Shep-pard/EtherCatIoBoard/EthercatIOBoard/EthercatIOBoard.kicad_sch

## KiCad design EthercatIOBoard/EthercatIOBoard.kicad_sch (2024-12-22)

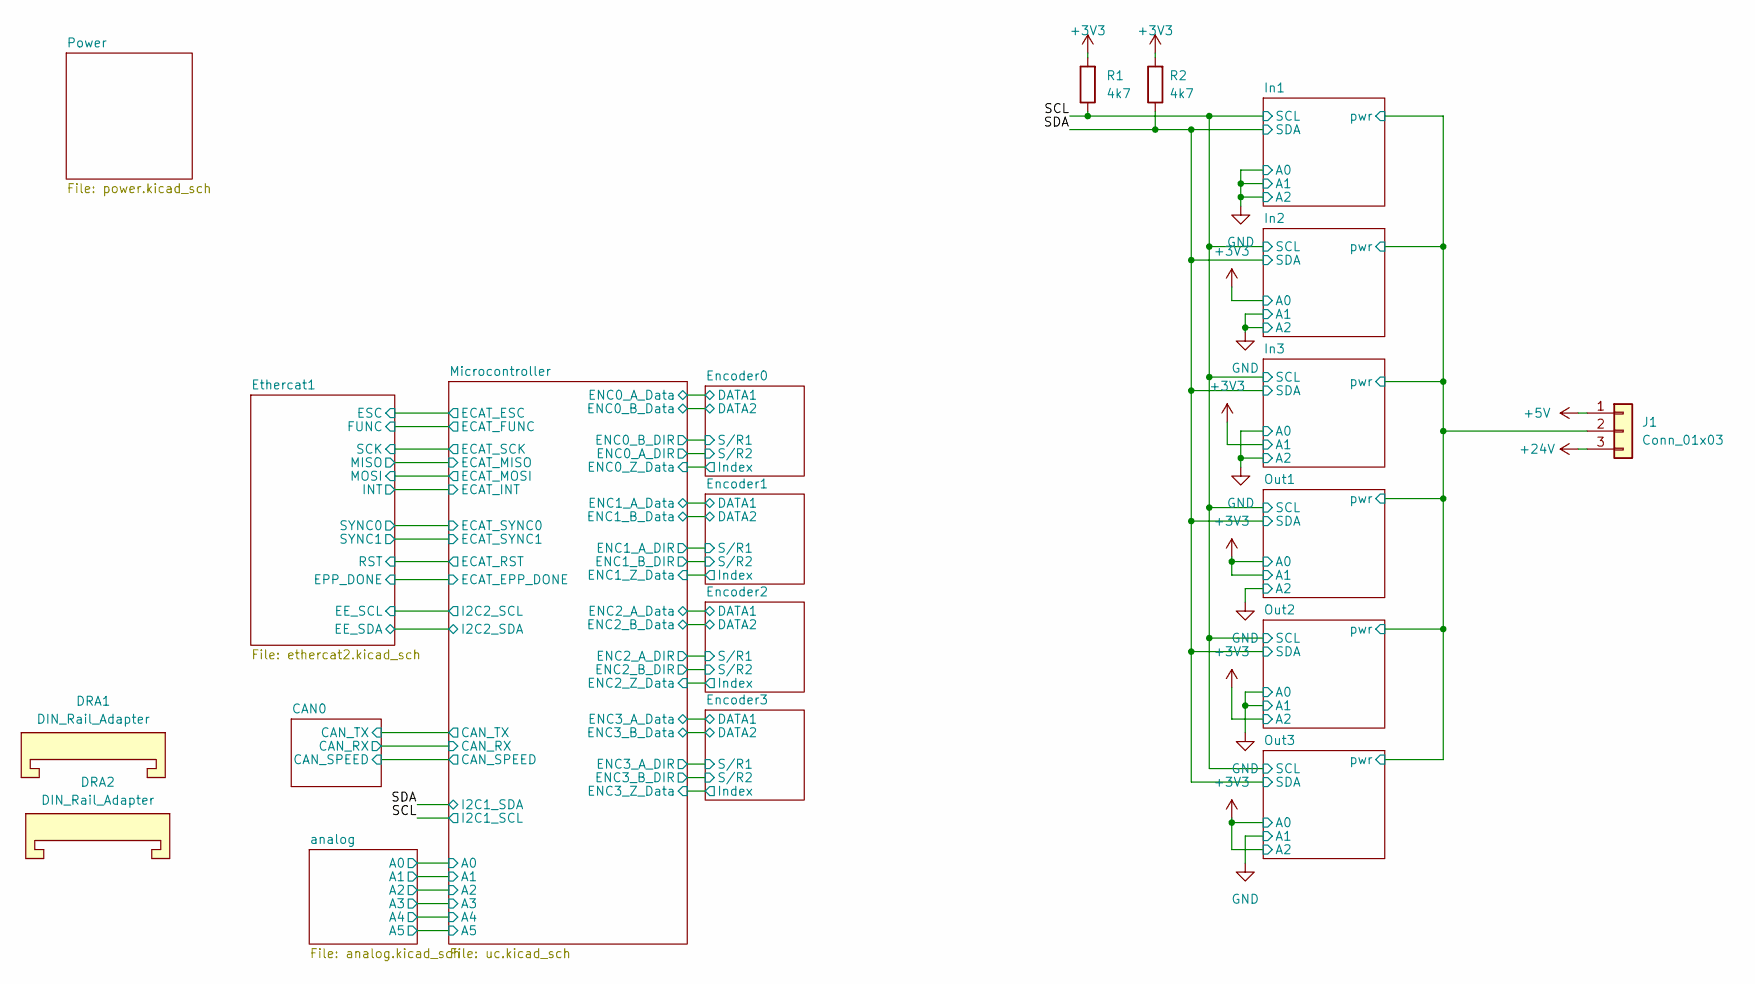
[picture p29: schematic EthercatIOBoard.kicad_sch]

Parts:
DRA1, DRA2: DIN_Rail_Adapter; DINRailAdapter_3xM3_PhoenixContact_1201578
J1: Conn_01x03; PinHeader_1x03_P2.54mm_Vertical_SMD_Pin1Right; JLC C780061
R1, R2: 4k7; R_0402_1005Metric; LCSC Part # C25900

Connections:
+3V3: R1.2, R2.2
+5V: J1.1
+24V: J1.3
SCL: R1.1
SDA: R2.1
pwr: J1.2
