Shep-pard/EtherCatIoBoard/EthercatIOBoard/analog.kicad_sch

## KiCad design EthercatIOBoard/analog.kicad_sch (2024-12-13)

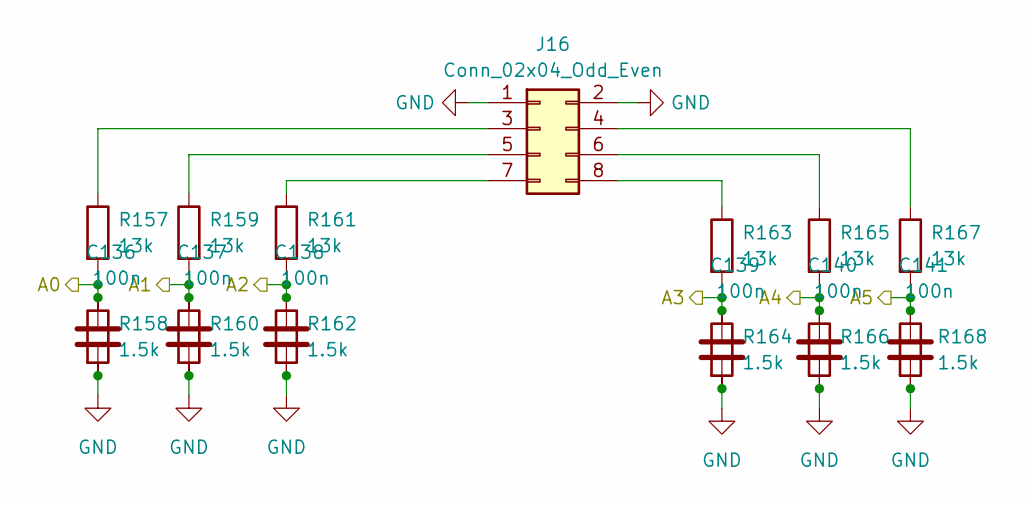
[picture p30: schematic analog.kicad_sch]

Parts:
C136, C137, C138, C139, C140, C141: 100n; C_0402_1005Metric; LCSC Part # C307331
J16: Conn_02x04_Odd_Even; 2Row4Pin3.5mm; LCSC Part # C2923127
R157, R159, R161, R163, R165, R167: 13k; R_0603_1608Metric; LCSC Part # C22797
R158, R160, R162: 1.5k; R_0603_1608Metric; LCSC Part # C22843
R164, R166, R168: 1.5k; R_0603_1608Metric; LCSC Part # C22797

Connections:
A0: C136.1, R157.2, R158.1
A1: C137.1, R159.2, R160.1
A2: C138.1, R161.2, R162.1
A3: C139.1, R163.2, R164.1
A4: C140.1, R165.2, R166.1
A5: C141.1, R167.2, R168.1
GND: C136.2, C137.2, C138.2, C139.2, C140.2, C141.2, J16.1, J16.2, R158.2, R160.2, R162.2, R164.2, R166.2, R168.2
unnamed: J16.3, R157.1
unnamed: J16.4, R167.1
unnamed: J16.5, R159.1
unnamed: J16.6, R165.1
unnamed: J16.7, R161.1
unnamed: J16.8, R163.1
