Shep-pard/EtherCatIoBoard/EthercatIOBoard/can.kicad_sch

## KiCad design EthercatIOBoard/can.kicad_sch (2024-12-13)

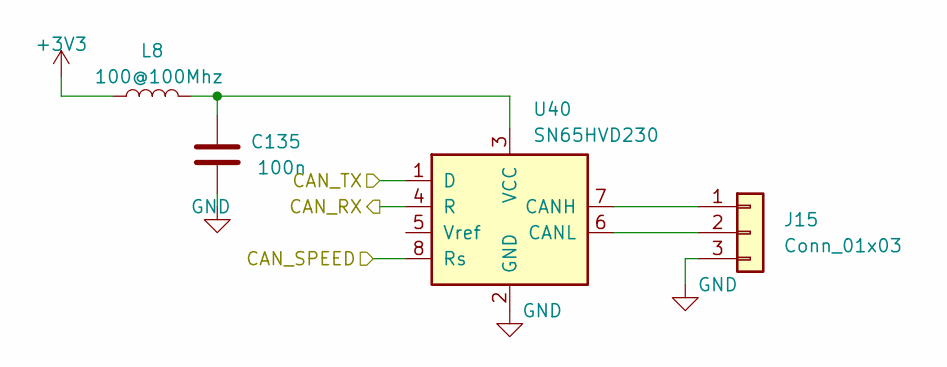
[picture p31: schematic can.kicad_sch]

Parts:
C135: 100n; C_0402_1005Metric; LCSC Part # C307331
J15: Conn_01x03; TerminalBlock_4Ucon_1x03_P3.50mm_Vertical; LCSC Part # C192778
L8: 100@100Mhz; R_0805_2012Metric; LCSC Part # C1015
U40: SN65HVD230; SOIC-8_3.9x4.9mm_P1.27mm; LCSC Part # C12084

Connections:
+3V3: L8.1
CAN_RX: U40.4 (R)
CAN_SPEED: U40.8 (Rs)
CAN_TX: U40.1 (D)
GND: C135.2, J15.3, U40.2 (GND)
unnamed: C135.1, L8.2, U40.3 (VCC)
unnamed: J15.1, U40.7 (CANH)
unnamed: J15.2, U40.6 (CANL)
