Shep-pard/EtherCatIoBoard/EthercatIOBoard/digIn.kicad_sch

## KiCad design EthercatIOBoard/digIn.kicad_sch (2024-12-13)

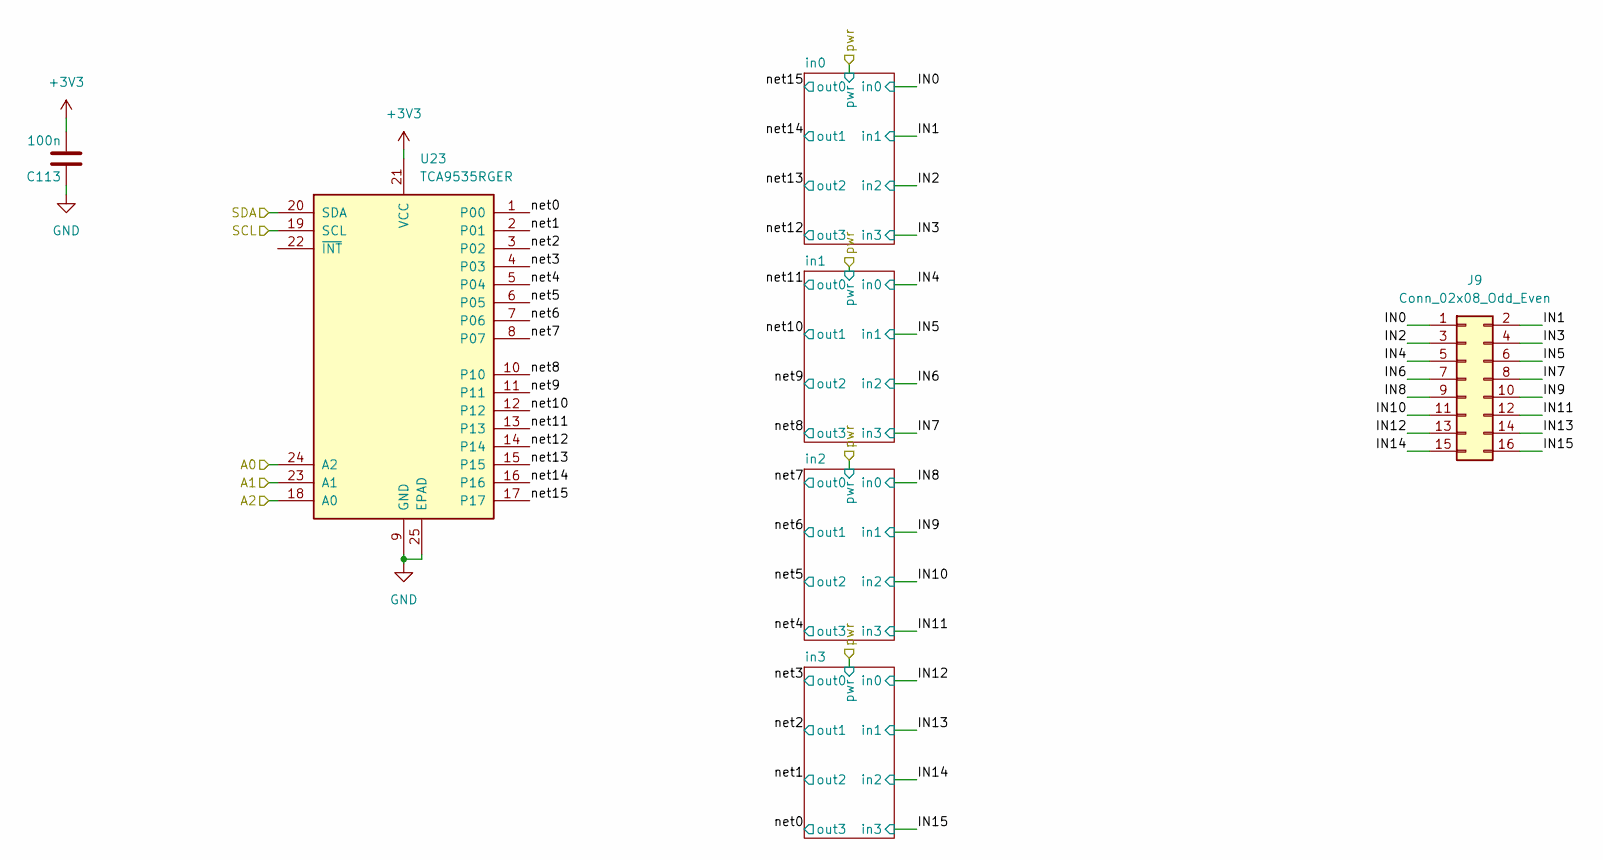
[picture p32: schematic digIn.kicad_sch]

Parts:
C113: 100n; C_0402_1005Metric; LCSC Part # C307331
J9: Conn_02x08_Odd_Even; 2Row8Pin3.5mm; LCSC Part # C2923113
U23: TCA9535RGER; VQFN-24-1EP_4x4mm_P0.5mm_EP2.45x2.45mm; JLC C527428

Connections:
+3V3: C113.2, U23.21 (VCC)
A0: U23.24 (A2)
A1: U23.23 (A1)
A2: U23.18 (A0)
GND: C113.1, U23.9 (GND), U23.25 (EPAD)
IN0: J9.1
IN1: J9.2
IN2: J9.3
IN3: J9.4
IN4: J9.5
IN5: J9.6
IN6: J9.7
IN7: J9.8
IN8: J9.9
IN9: J9.10
IN10: J9.11
IN11: J9.12
IN12: J9.13
IN13: J9.14
IN14: J9.15
IN15: J9.16
SCL: U23.19 (SCL)
SDA: U23.20 (SDA)
net0: U23.1 (P00)
net1: U23.2 (P01)
net2: U23.3 (P02)
net3: U23.4 (P03)
net4: U23.5 (P04)
net5: U23.6 (P05)
net6: U23.7 (P06)
net7: U23.8 (P07)
net8: U23.10
net9: U23.11
net10: U23.12
net11: U23.13
net12: U23.14
net13: U23.15
net14: U23.16
net15: U23.17
