Shep-pard/EtherCatIoBoard/EthercatIOBoard/digInSingle.kicad_sch

## KiCad design EthercatIOBoard/digInSingle.kicad_sch (2024-12-13)

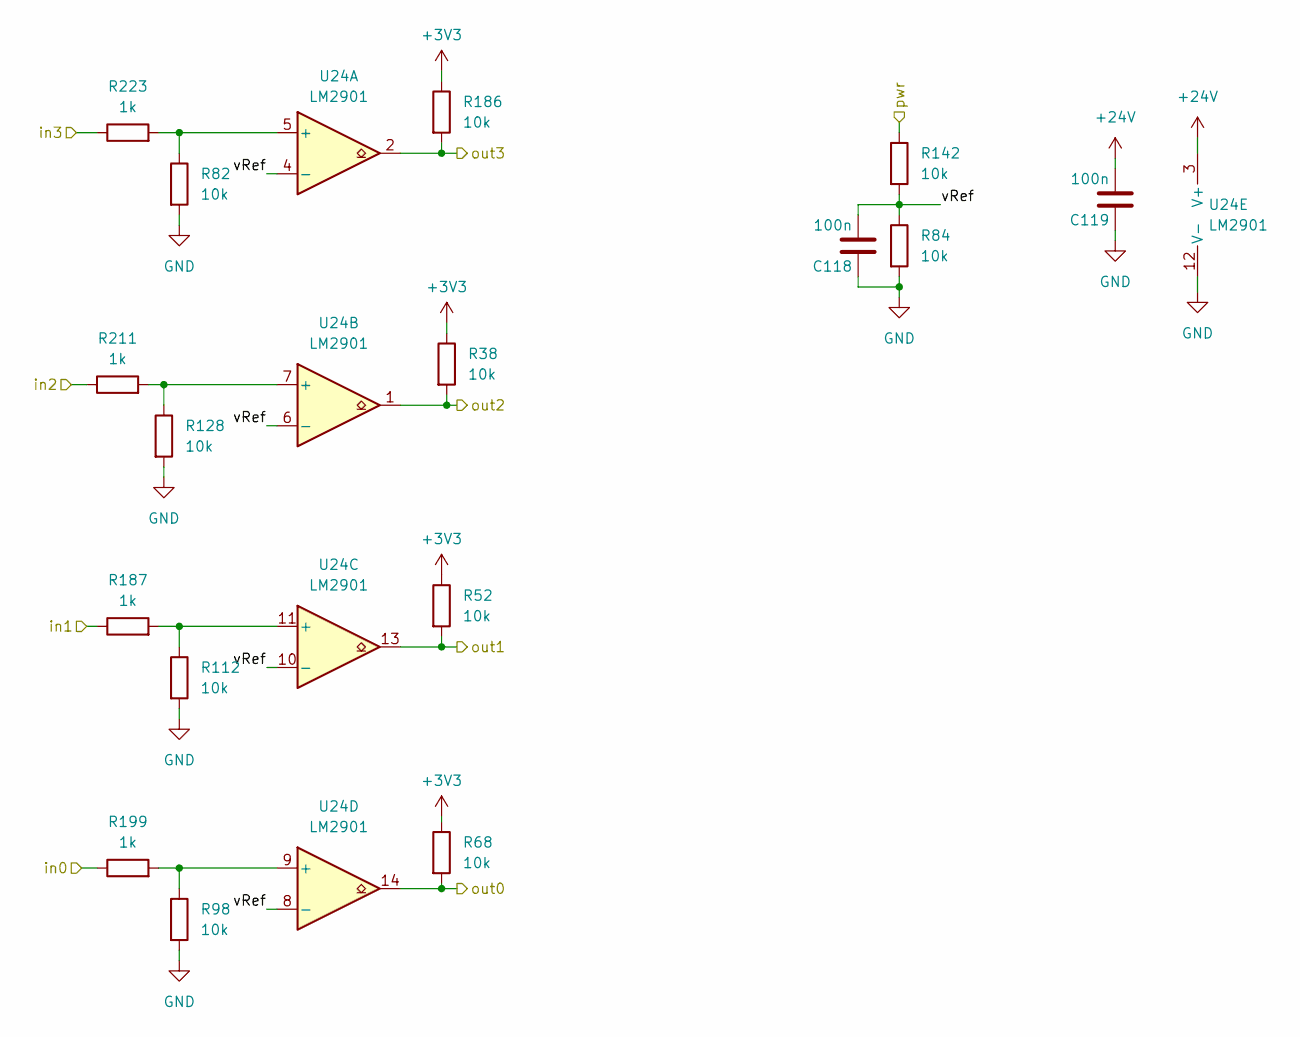
[picture p33: schematic digInSingle.kicad_sch]

Parts:
C118, C119: 100n; C_0402_1005Metric; LCSC Part # C307331
R38, R52, R68, R82, R84, R98, R112, R128, R142, R186: 10k; C_0402_1005Metric; LCSC Part # C25744
R187, R199, R211, R223: 1k; C_0402_1005Metric; LCSC Part # C11702
U24: LM2901; SO-14_3.9x8.65mm_P1.27mm; LCSC Part # C5145307

Connections:
+3V3: R38.1, R52.1, R68.1, R186.1
+24V: C119.2, U24.3 (V+)
GND: C118.1, C119.1, R82.2, R84.2, R98.2, R112.2, R128.2, U24.12 (V-)
unnamed: R112.1, R187.2, U24.11 (+)
unnamed: R128.1, R211.2, U24.7 (+)
unnamed: R98.1, R199.2, U24.9 (+)
unnamed: R82.1, R223.2, U24.5 (+)
in0: R199.1
in1: R187.1
in2: R211.1
in3: R223.1
out0: R68.2, U24.14
out1: R52.2, U24.13
out2: R38.2, U24.1
out3: R186.2, U24.2
pwr: R142.1
vRef: C118.2, R84.1, R142.2, U24.4 (-), U24.6 (-), U24.8 (-), U24.10 (-)
