Shep-pard/EtherCatIoBoard/EthercatIOBoard/digOut.kicad_sch

## KiCad design EthercatIOBoard/digOut.kicad_sch (2024-12-13)

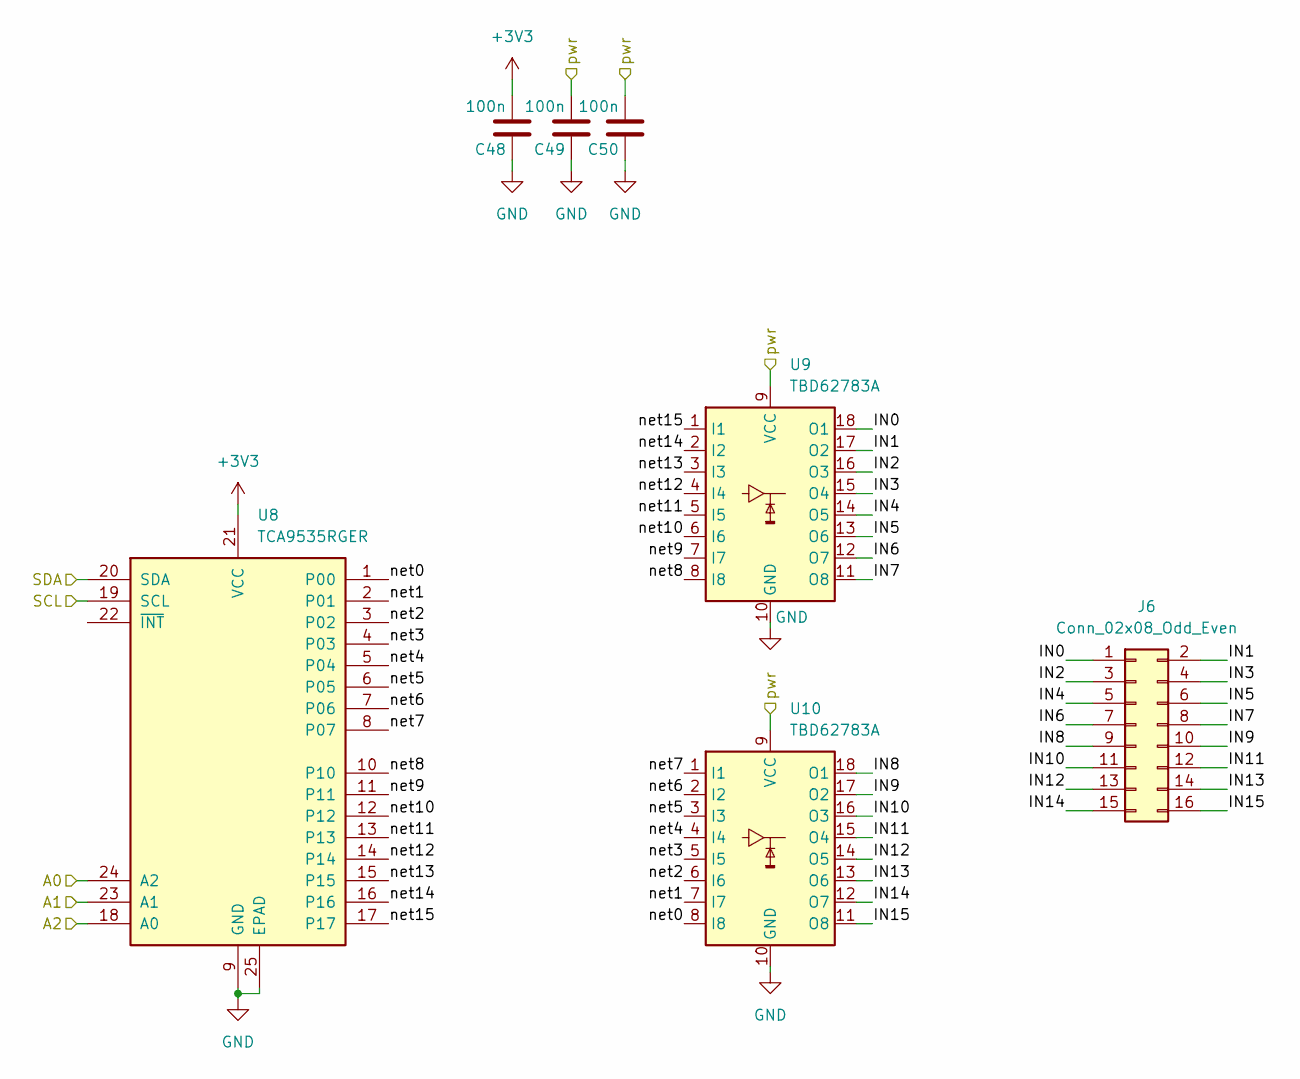
[picture p34: schematic digOut.kicad_sch]

Parts:
C48, C49, C50: 100n; C_0402_1005Metric; LCSC Part # C307331
J6: Conn_02x08_Odd_Even; 2Row8Pin3.5mm; LCSC Part # C2923113
U8: TCA9535RGER; VQFN-24-1EP_4x4mm_P0.5mm_EP2.45x2.45mm; JLC C527428
U9, U10: TBD62783A; SOP-18_7x12.5mm_P1.27mm; JLCRotOffset -90

Connections:
+3V3: C48.2, U8.21 (VCC)
A0: U8.24 (A2)
A1: U8.23 (A1)
A2: U8.18 (A0)
GND: C48.1, C49.1, C50.1, U8.9 (GND), U8.25 (EPAD), U9.10 (GND), U10.10 (GND)
IN0: J6.1, U9.18 (O1)
IN1: J6.2, U9.17 (O2)
IN2: J6.3, U9.16 (O3)
IN3: J6.4, U9.15 (O4)
IN4: J6.5, U9.14 (O5)
IN5: J6.6, U9.13 (O6)
IN6: J6.7, U9.12 (O7)
IN7: J6.8, U9.11 (O8)
IN8: J6.9, U10.18 (O1)
IN9: J6.10, U10.17 (O2)
IN10: J6.11, U10.16 (O3)
IN11: J6.12, U10.15 (O4)
IN12: J6.13, U10.14 (O5)
IN13: J6.14, U10.13 (O6)
IN14: J6.15, U10.12 (O7)
IN15: J6.16, U10.11 (O8)
SCL: U8.19 (SCL)
SDA: U8.20 (SDA)
net0: U8.1 (P00), U10.8 (I8)
net1: U8.2 (P01), U10.7 (I7)
net2: U8.3 (P02), U10.6 (I6)
net3: U8.4 (P03), U10.5 (I5)
net4: U8.5 (P04), U10.4 (I4)
net5: U8.6 (P05), U10.3 (I3)
net6: U8.7 (P06), U10.2 (I2)
net7: U8.8 (P07), U10.1 (I1)
net8: U8.10, U9.8 (I8)
net9: U8.11, U9.7 (I7)
net10: U8.12, U9.6 (I6)
net11: U8.13, U9.5 (I5)
net12: U8.14, U9.4 (I4)
net13: U8.15, U9.3 (I3)
net14: U8.16, U9.2 (I2)
net15: U8.17, U9.1 (I1)
pwr: C49.2, C50.2, U9.9 (VCC), U10.9 (VCC)
