Shep-pard/EtherCatIoBoard/EthercatIOBoard/encoderIn.kicad_sch

## KiCad design EthercatIOBoard/encoderIn.kicad_sch (2024-12-14)

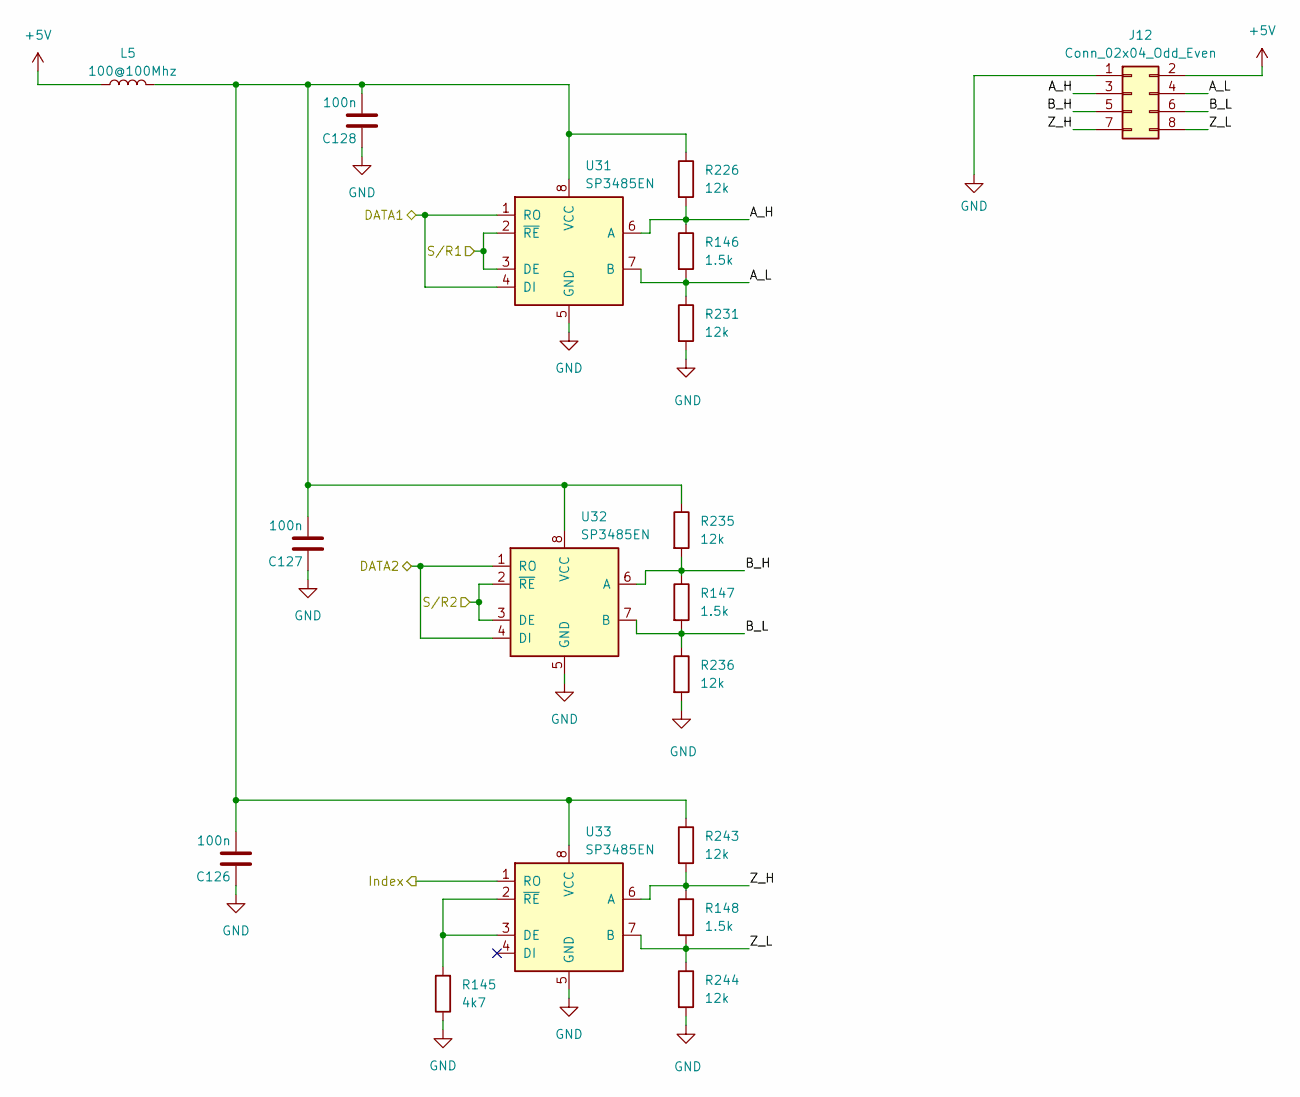
[picture p35: schematic encoderIn.kicad_sch]

Parts:
C126, C127, C128: 100n; C_0402_1005Metric; LCSC Part # C307331
J12: Conn_02x04_Odd_Even; 2Row4Pin3.5mm; LCSC Part # C2923127
L5: 100@100Mhz; R_0805_2012Metric; LCSC Part # C1015
R145: 4k7; R_0402_1005Metric; LCSC Part # C25900
R146, R147, R148: 1.5k; R_0603_1608Metric; LCSC Part # C22787
R226, R231, R235, R236, R243, R244: 12k; R_0402_1005Metric; LCSC Part # C25752
U31, U32, U33: SP3485EN; SOIC-8_3.9x4.9mm_P1.27mm; LCSC Part # C6855

Connections:
+5V: J12.2, L5.1
A_H: J12.3, R146.1, R226.2, U31.6 (A)
A_L: J12.4, R146.2, R231.1, U31.7 (B)
B_H: J12.5, R147.1, R235.2, U32.6 (A)
B_L: J12.6, R147.2, R236.1, U32.7 (B)
DATA1: U31.1 (RO), U31.4 (DI)
DATA2: U32.1 (RO), U32.4 (DI)
GND: C126.1, C127.1, C128.1, J12.1, R145.1, R231.2, R236.2, R244.2, U31.5 (GND), U32.5 (GND), U33.5 (GND)
Index: U33.1 (RO)
unnamed: C126.2, C127.2, C128.2, L5.2, R226.1, R235.1, R243.1, U31.8 (VCC), U32.8 (VCC), U33.8 (VCC)
unnamed: R145.2, U33.2 (~RE), U33.3 (DE)
S/R1: U31.2 (~RE), U31.3 (DE)
S/R2: U32.2 (~RE), U32.3 (DE)
Z_H: J12.7, R148.1, R243.2, U33.6 (A)
Z_L: J12.8, R148.2, R244.1, U33.7 (B)
