Shep-pard/EtherCatIoBoard/EthercatIOBoard/ethercat2.kicad_sch

## KiCad design EthercatIOBoard/ethercat2.kicad_sch (2024-12-15)

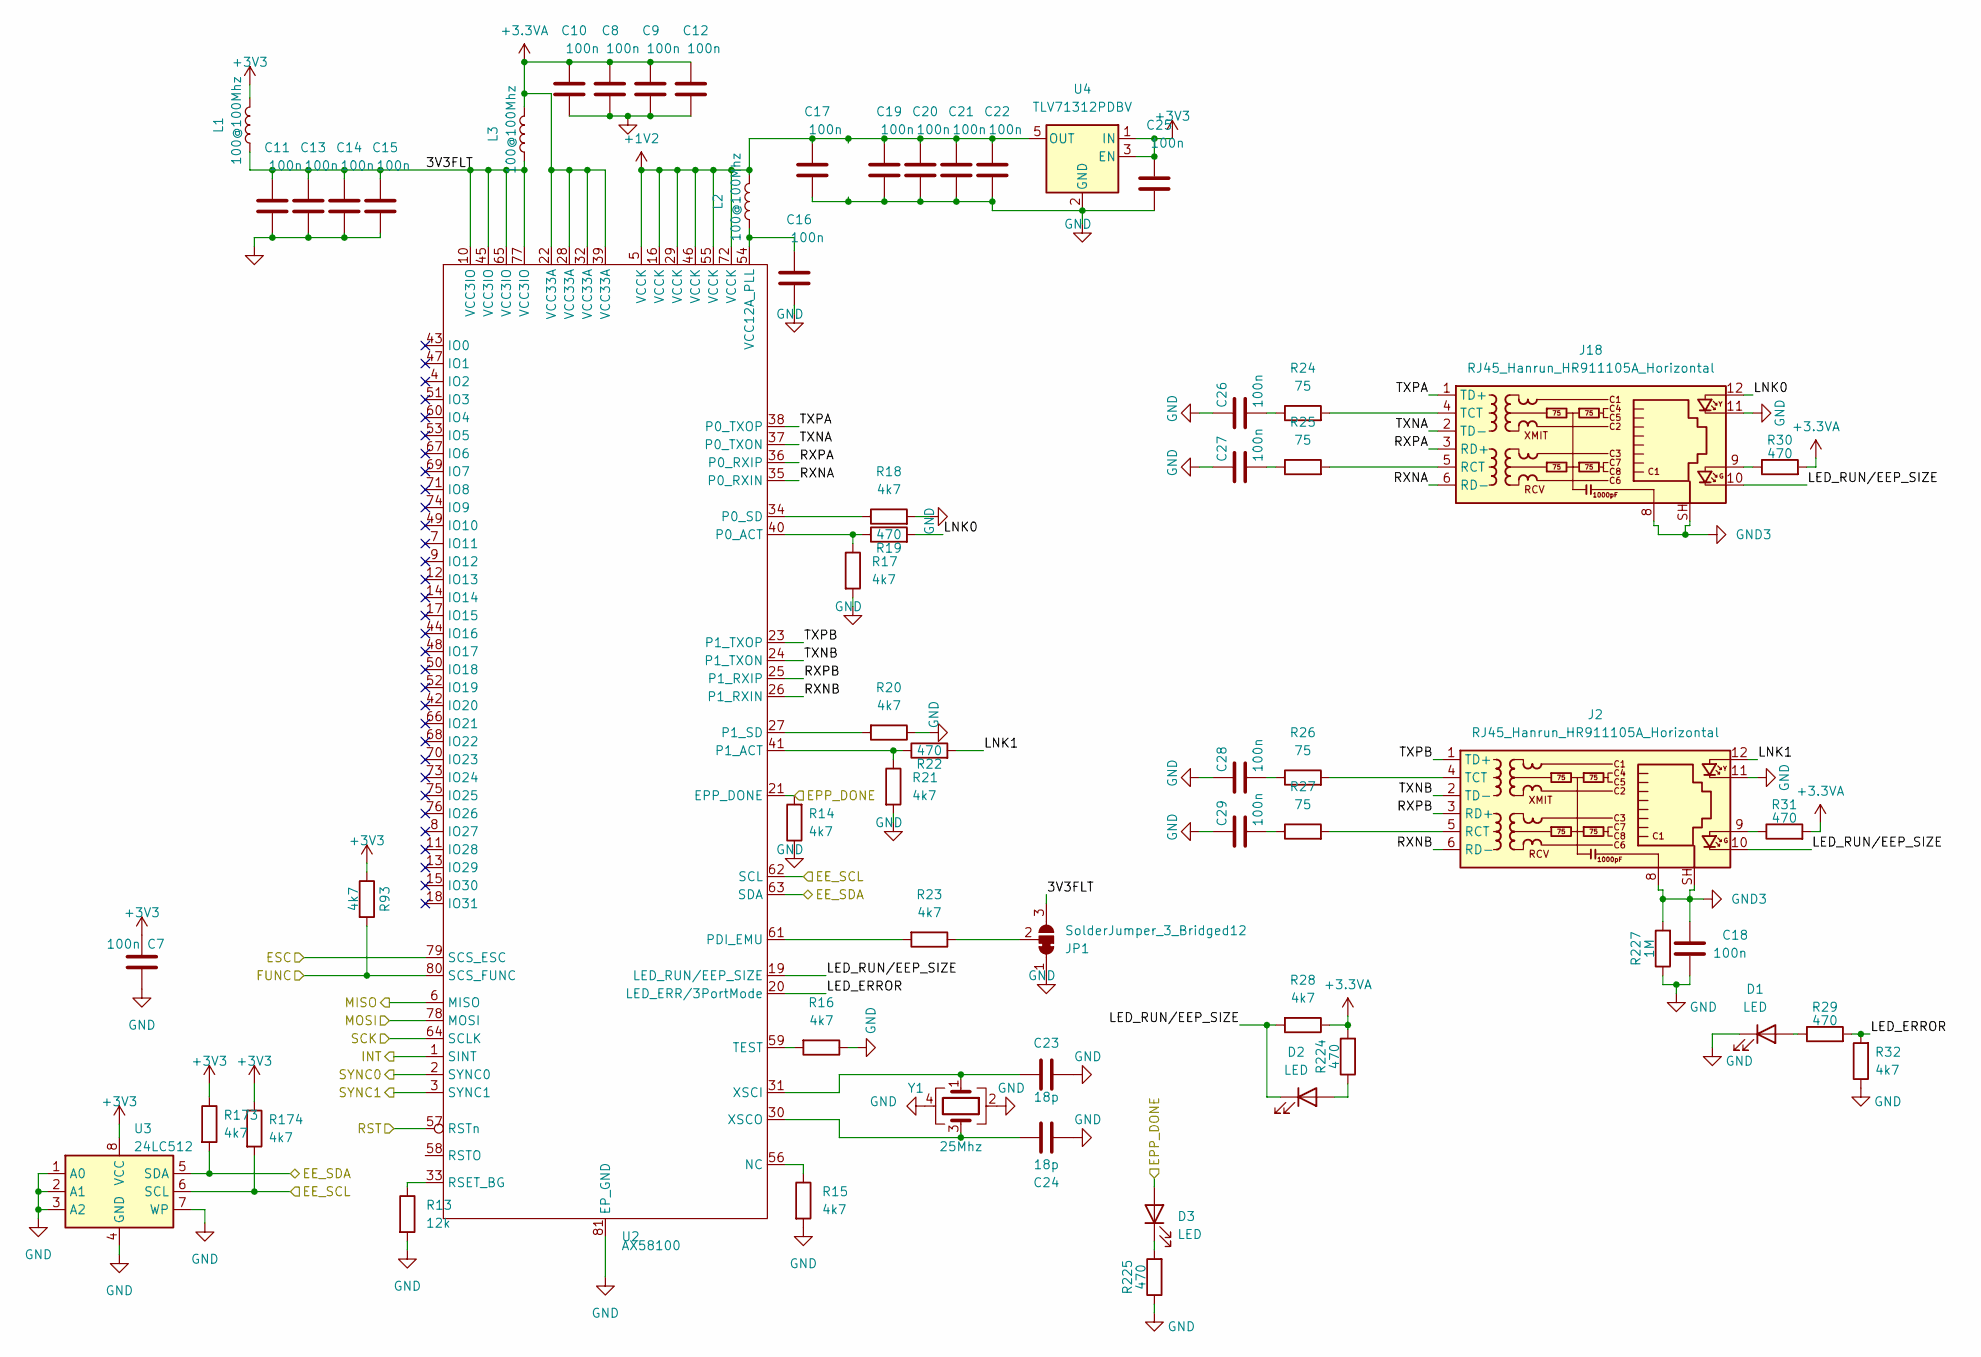
[picture p36: schematic ethercat2.kicad_sch]

Parts:
C7, C8, C9, C10, C11, C12, C13, C14, C15, C16, C17, C19, C20, C21, C22, C25, C26, C27, C28, C29: 100n; C_0402_1005Metric; LCSC Part # C307331
C18: 100n; C_1206_3216Metric; LCSC Part # C307331
C23, C24: 18p; C_0402_1005Metric; LCSC Part # C1549
D1, D2, D3: LED; LED_0603_1608Metric; JLC C2286
J2, J18: RJ45_Hanrun_HR911105A_Horizontal; LCSC Part # C12074
JP1: SolderJumper_3_Bridged12; SolderJumper-3_P1.3mm_Bridged2Bar12_RoundedPad1.0x1.5mm
L1, L2, L3: 100@100Mhz; R_0805_2012Metric; LCSC Part # C1015
R13: 12k; R_0402_1005Metric; LCSC Part # C25752
R14, R15, R16, R17, R18, R20, R21, R23, R28, R32, R93, R173, R174: 4k7; R_0402_1005Metric; LCSC Part # C25900
R19, R22, R29, R30, R31, R224, R225: 470; R_0402_1005Metric; LCSC Part # C25117
R24, R25, R26, R27: 75; R_0603_1608Metric; LCSC Part # C4275
R227: 1M; C_0805_2012Metric; LCSC Part # C17514
U2: AX58100; LQFP-80_10x10mm_P0.4mm_EP
U3: 24LC512; SO-8_3.9x4.9mm_P1.27mm; LCSC Part # C2987264
U4: TLV71312PDBV; SOT-23-5; LCSC Part # C2872351
Y1: 25Mhz; Crystal_SMD_3225-4Pin_3.2x2.5mm; LCSC Part # C9006

Connections:
3V3FLT: C11.1, C13.1, C14.1, C15.1, JP1.3 (B), L1.1, L3.1, U2.10 (VCC3IO), U2.45 (VCC3IO), U2.65 (VCC3IO), U2.77 (VCC3IO)
+1V2: C17.1, C19.1, C20.1, C21.1, C22.1, L2.2, U2.5 (VCCK), U2.16 (VCCK), U2.29 (VCCK), U2.46 (VCCK), U2.55 (VCCK), U2.72 (VCCK), U4.5 (OUT)
+3.3VA: C8.1, C9.1, C10.1, C12.1, L3.2, R28.1, R30.2, R31.2, R224.2, U2.22 (VCC33A), U2.28 (VCC33A), U2.32 (VCC33A), U2.39 (VCC33A)
+3V3: C7.1, C25.1, L1.2, R93.1, R173.1, R174.1, U3.8 (VCC), U4.1 (IN), U4.3 (EN)
EE_SCL: R174.2, U2.62 (SCL), U3.6 (SCL)
EE_SDA: R173.2, U2.63 (SDA), U3.5 (SDA)
EPP_DONE: D3.2 (A), R14.2, U2.21 (EPP_DONE)
ESC: U2.79 (SCS_ESC)
FUNC: R93.2, U2.80 (SCS_FUNC)
GND: C7.2, C8.2, C9.2, C10.2, C11.2, C12.2, C13.2, C14.2, C15.2, C16.2, C17.2, C18.2, C19.2, C20.2, C21.2, C22.2, C23.1, C24.1, C25.2, C26.1, C27.1, C28.1, C29.1, D1.1 (K), J2.11, J18.11, JP1.1 (A), R13.2, R14.1, R15.2, R16.1, R17.2, R18.2, R20.1, R21.2, R32.1, R225.1, R227.1, U2.81 (EP_GND), U3.1 (A0), U3.2 (A1), U3.3 (A2), U3.4 (GND), U3.7 (WP), U4.2 (GND), Y1.2, Y1.4
GND3: C18.1, J2.8, J2.SH, J18.8, J18.SH, R227.2
INT: U2.1 (SINT)
LED_ERROR: R29.2, R32.2, U2.20 (LED_ERR/3PortMode)
LED_RUN/EEP_SIZE: D2.1 (K), J2.10, J18.10, R28.2, U2.19 (LED_RUN/EEP_SIZE)
LNK0: J18.12, R19.2
LNK1: J2.12, R22.2
MISO: U2.6 (MISO)
MOSI: U2.78 (MOSI)
unnamed: C16.1, L2.1, U2.54 (VCC12A_PLL)
unnamed: C23.2, U2.31 (XSCI), Y1.1
unnamed: C24.2, U2.30 (XSCO), Y1.3
unnamed: C26.2, R24.1
unnamed: C27.2, R25.1
unnamed: C28.2, R26.1
unnamed: C29.2, R27.1
unnamed: D1.2 (A), R29.1
unnamed: D2.2 (A), R224.1
unnamed: D3.1 (K), R225.2
unnamed: J2.4 (TCT), R26.2
unnamed: J2.5 (RCT), R27.2
unnamed: J2.9, R31.1
unnamed: J18.4 (TCT), R24.2
unnamed: J18.5 (RCT), R25.2
unnamed: J18.9, R30.1
unnamed: JP1.2 (C), R23.1
unnamed: R13.1, U2.33 (RSET_BG)
unnamed: R15.1, U2.56 (NC)
unnamed: R16.2, U2.59 (TEST)
unnamed: R17.1, R19.1, U2.40 (P0_ACT)
unnamed: R18.1, U2.34 (P0_SD)
unnamed: R20.2, U2.27 (P1_SD)
unnamed: R21.1, R22.1, U2.41 (P1_ACT)
unnamed: R23.2, U2.61 (PDI_EMU)
RST: U2.57 (RSTn)
RXNA: J18.6 (RD-), U2.35 (P0_RXIN)
RXNB: J2.6 (RD-), U2.26 (P1_RXIN)
RXPA: J18.3 (RD+), U2.36 (P0_RXIP)
RXPB: J2.3 (RD+), U2.25 (P1_RXIP)
SCK: U2.64 (SCLK)
SYNC0: U2.2 (SYNC0)
SYNC1: U2.3 (SYNC1)
TXNA: J18.2 (TD-), U2.37 (P0_TXON)
TXNB: J2.2 (TD-), U2.24 (P1_TXON)
TXPA: J18.1 (TD+), U2.38 (P0_TXOP)
TXPB: J2.1 (TD+), U2.23 (P1_TXOP)
