Shep-pard/EtherCatIoBoard/EthercatIOBoard/ethercat.kicad_sch

## KiCad design EthercatIOBoard/ethercat.kicad_sch (2024-12-13)

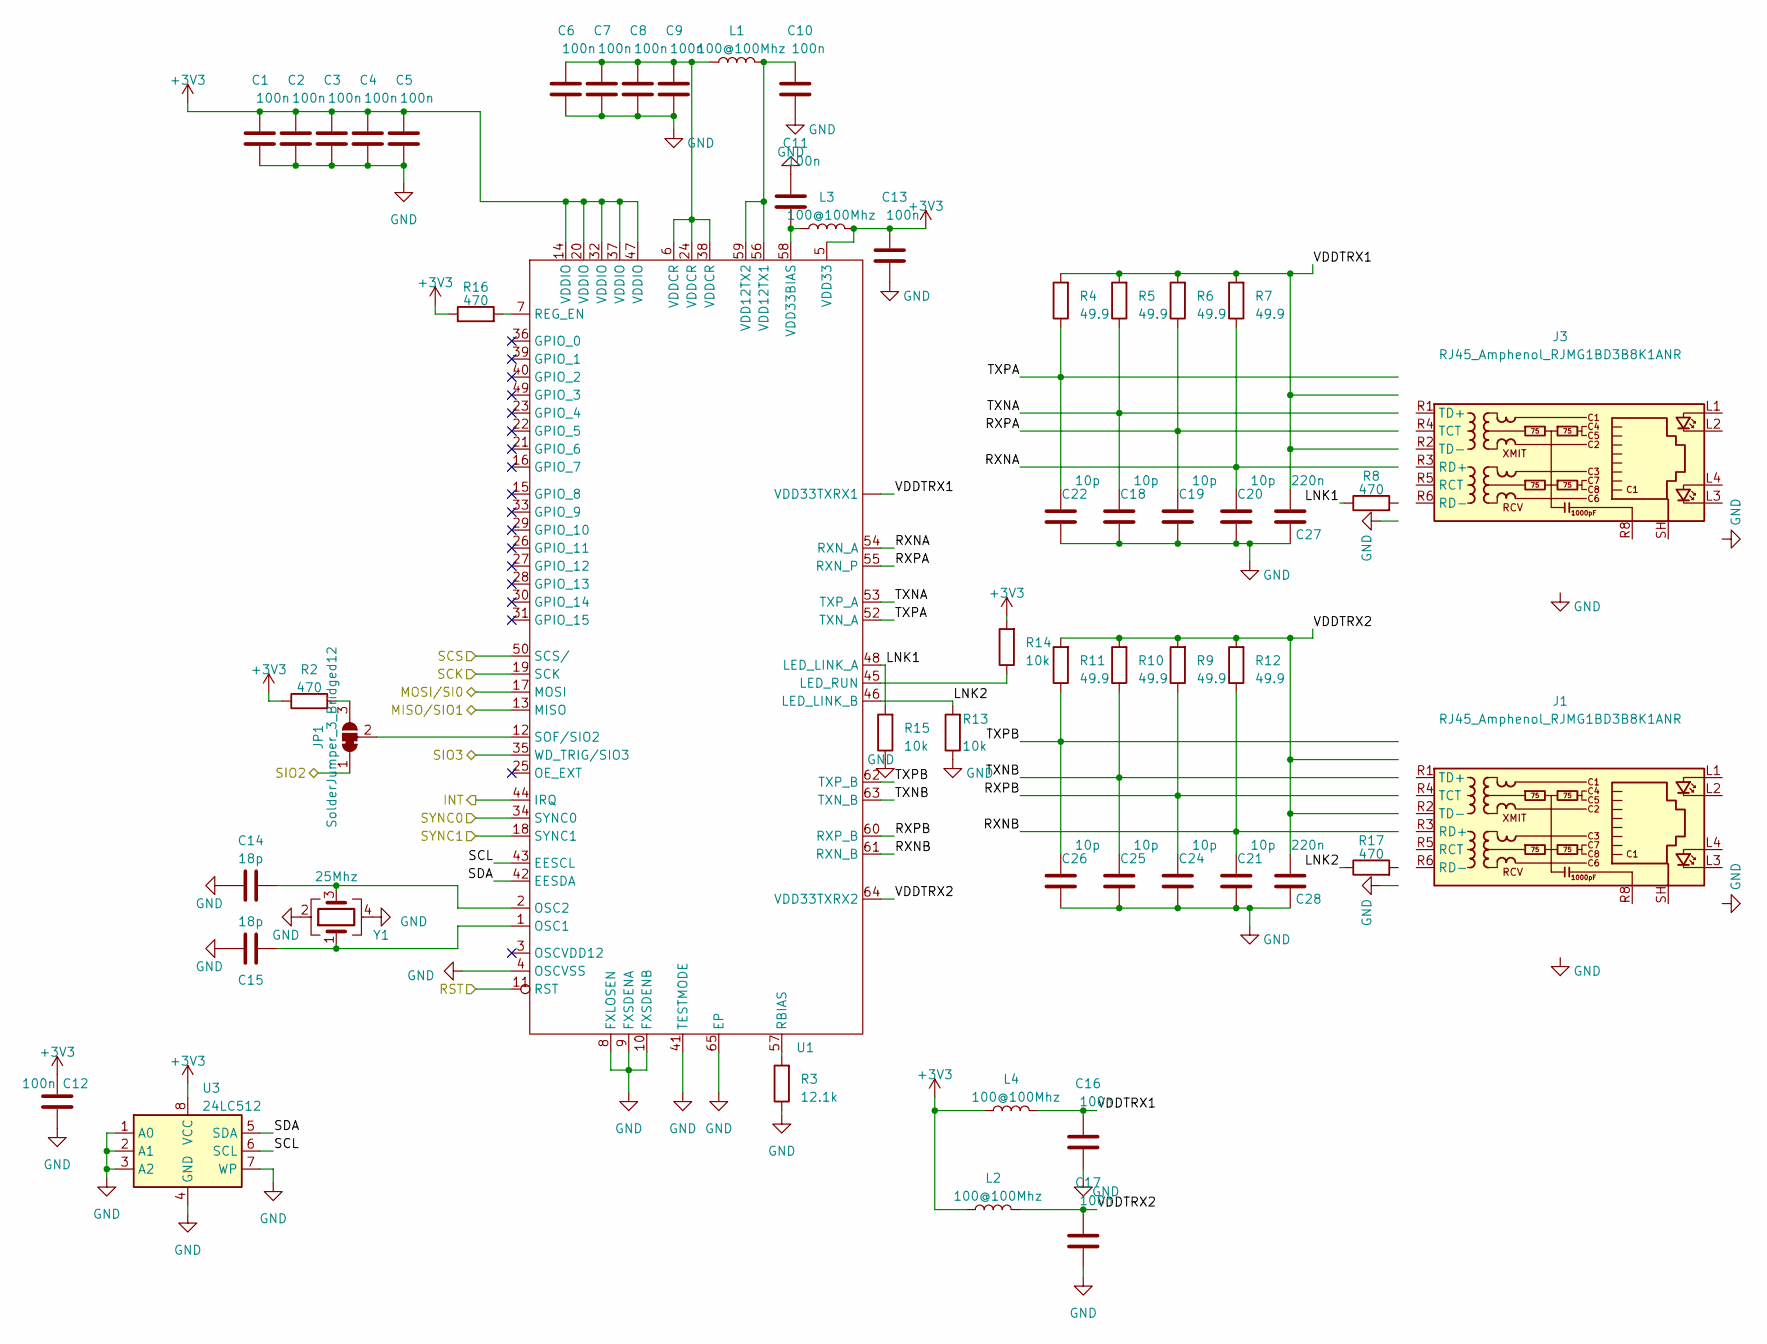
[picture p37: schematic ethercat.kicad_sch]

Parts:
C1, C2, C3, C4, C5, C6, C7, C8, C9, C10, C11, C12, C16, C17: 100n; C_0402_1005Metric; LCSC Part # C307331
C13: 100n
C14, C15: 18p; C_0402_1005Metric; LCSC Part # C1549
C18, C19, C20, C21, C22, C24, C25, C26: 10p; C_0402_1005Metric; LCSC Part # C1547
C27, C28: 220n; C_0402_1005Metric; LCSC Part # C16772
J1, J3: RJ45_Amphenol_RJMG1BD3B8K1ANR
JP1: SolderJumper_3_Bridged12
L1, L2, L3, L4: 100@100Mhz; R_0805_2012Metric; LCSC Part # C1015
R2: 470
R3: 12.1k; R_0402_1005Metric; LCSC Part # C25852
R4, R5, R6, R7, R9, R10, R11, R12: 49.9; R_0402_1005Metric; LCSC Part # C25120
R8, R16, R17: 470; R_0402_1005Metric; LCSC Part # C25117
R13, R14, R15: 10k; R_0402_1005Metric; LCSC Part # C25744
U1: (no value)
U3: 24LC512
Y1: 25Mhz; Crystal_SMD_3225-4Pin_3.2x2.5mm; LCSC Part # X322525MOB4SI

Connections:
+3V3: C1.1, C2.1, C3.1, C4.1, C5.1, C12.1, C13.1, L2.1, L3.2, L4.1, R2.1, R14.2, R16.1, U1.5 (VDD33), U1.14 (VDDIO), U1.20 (VDDIO), U1.32 (VDDIO), U1.37 (VDDIO), U1.47 (VDDIO), U3.8 (VCC)
GND: C1.2, C2.2, C3.2, C4.2, C5.2, C6.2, C7.2, C8.2, C9.2, C10.2, C11.1, C12.2, C13.2, C14.1, C15.1, C16.2, C17.2, C18.2, C19.2, C20.2, C21.2, C22.2, C24.2, C25.2, C26.2, C27.2, C28.2, R3.1, R13.1, R15.1, U1.4 (OSCVSS), U1.8 (FXLOSEN), U1.9 (FXSDENA), U1.10 (FXSDENB), U1.41 (TESTMODE), U1.65 (EP), U3.1 (A0), U3.2 (A1), U3.3 (A2), U3.4 (GND), U3.7 (WP), Y1.2, Y1.4
INT: U1.44 (IRQ)
LNK1: R8.1, R15.2, U1.48 (LED_LINK_A)
LNK2: R13.2, R17.1, U1.46 (LED_LINK_B)
MISO/SIO1: U1.13 (MISO)
MOSI/SI0: U1.17 (MOSI)
unnamed: C6.1, C7.1, C8.1, C9.1, L1.1, U1.6 (VDDCR), U1.24 (VDDCR), U1.38 (VDDCR)
unnamed: C10.1, L1.2, U1.56 (VDD12TX1), U1.59 (VDD12TX2)
unnamed: C11.2, L3.1, U1.58 (VDD33BIAS)
unnamed: C14.2, U1.2 (OSC2), Y1.3
unnamed: C15.2, U1.1 (OSC1), Y1.1
unnamed: JP1.2 (C), U1.12 (SOF/SIO2)
unnamed: JP1.3 (B), R2.2
unnamed: R3.2, U1.57 (RBIAS)
unnamed: R14.1, U1.45 (LED_RUN)
unnamed: R16.2, U1.7 (REG_EN)
RST: U1.11 (RST)
RXNA: C20.1, R7.1, U1.54 (RXN_A)
RXNB: C21.1, R12.1, U1.61 (RXN_B)
RXPA: C19.1, R6.1, U1.55 (RXN_P)
RXPB: C24.1, R9.1, U1.60 (RXP_B)
SCK: U1.19 (SCK)
SCL: U1.43 (EESCL), U3.6 (SCL)
SCS: U1.50 (SCS/)
SDA: U1.42 (EESDA), U3.5 (SDA)
SIO2: JP1.1 (A)
SIO3: U1.35 (WD_TRIG/SIO3)
SYNC0: U1.34 (SYNC0)
SYNC1: U1.18 (SYNC1)
TXNA: C18.1, R5.1, U1.53 (TXP_A)
TXNB: C25.1, R10.1, U1.63 (TXN_B)
TXPA: C22.1, R4.1, U1.52 (TXN_A)
TXPB: C26.1, R11.1, U1.62 (TXP_B)
VDDTRX1: C16.1, C27.1, L4.2, R4.2, R5.2, R6.2, R7.2, U1. (VDD33TXRX1)
VDDTRX2: C17.1, C28.1, L2.2, R9.2, R10.2, R11.2, R12.2, U1.64 (VDD33TXRX2)
