Shep-pard/EtherCatIoBoard/EthercatIOBoard/power.kicad_sch

## KiCad design EthercatIOBoard/power.kicad_sch (2024-12-13)

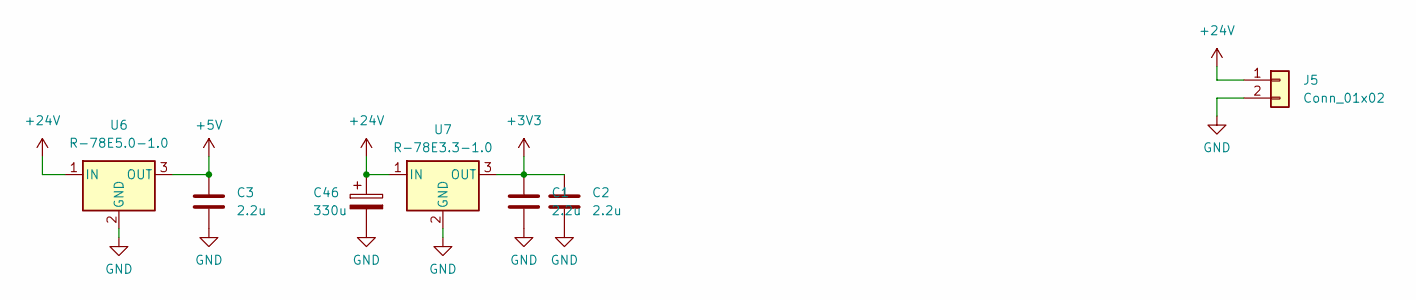
[picture p38: schematic power.kicad_sch]

Parts:
C1, C2, C3: 2.2u; R_0805_2012Metric; JLCPCB C377773
C46: 330u; CP_Elec_10x10.5; JLCPCB C5155333
J5: Conn_01x02; Wago_734-132_1x02_P3.50mm_Vertical
U6: R-78E5.0-1.0; Converter_DCDC_RECOM_R-78E-0.5_THT
U7: R-78E3.3-1.0; Converter_DCDC_RECOM_R-78E-0.5_THT

Connections:
+3V3: C1.1, C2.1, U7.3 (OUT)
+5V: C3.1, U6.3 (OUT)
+24V: C46.1, J5.1, U6.1 (IN), U7.1 (IN)
GND: C1.2, C2.2, C3.2, C46.2, J5.2, U6.2 (GND), U7.2 (GND)
