Shep-pard/EtherCatIoBoard/EthercatIOBoard/uc.kicad_sch

## KiCad design EthercatIOBoard/uc.kicad_sch (2024-12-13)

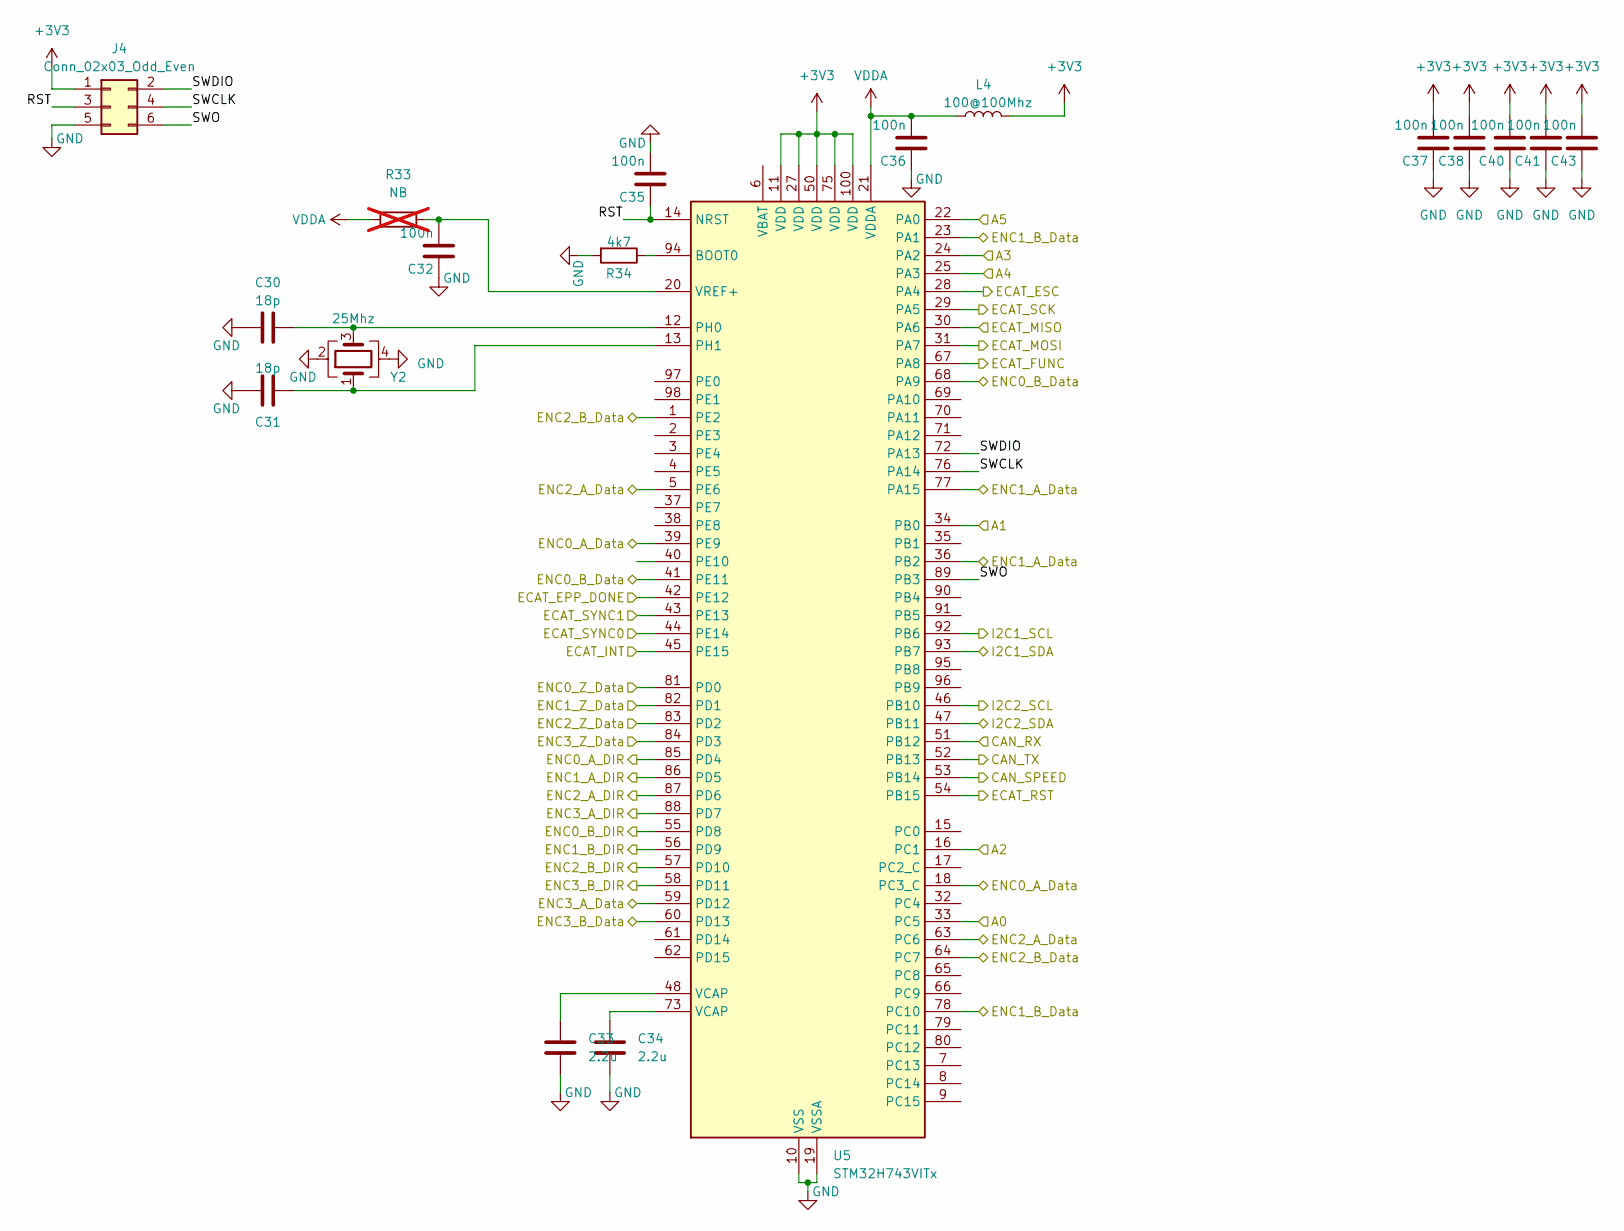
[picture p39: schematic uc.kicad_sch]

Parts:
C30, C31: 18p; C_0402_1005Metric; LCSC Part # C1549
C32, C35, C36, C37, C38, C40, C41, C43: 100n; C_0402_1005Metric; LCSC Part # C307331
C33, C34: 2.2u; R_0805_2012Metric; LCSC Part # C377773
J4: Conn_02x03_Odd_Even; PinHeader_2x03_P2.54mm_Vertical; JLCRotOffset -90
L4: 100@100Mhz; R_0805_2012Metric; LCSC Part # C1015
R33: NB; R_01005_0402Metric; not fitted
R34: 4k7; R_0402_1005Metric; LCSC Part # C25900
U5: STM32H743VITx; LQFP-100_14x14mm_P0.5mm; LCSC Part # C730183
Y2: 25Mhz; Crystal_SMD_3225-4Pin_3.2x2.5mm; LCSC Part # C9006

Connections:
+3V3: C37.2, C38.2, C40.2, C41.2, C43.2, J4.1, L4.2, U5.11 (VDD), U5.27 (VDD), U5.50 (VDD), U5.75 (VDD), U5.100 (VDD)
A0: U5.33 (PC5)
A1: U5.34 (PB0)
A2: U5.16 (PC1)
A3: U5.24 (PA2)
A4: U5.25 (PA3)
A5: U5.22 (PA0)
CAN_RX: U5.51 (PB12)
CAN_SPEED: U5.53 (PB14)
CAN_TX: U5.52 (PB13)
ECAT_EPP_DONE: U5.42 (PE12)
ECAT_ESC: U5.28 (PA4)
ECAT_FUNC: U5.67 (PA8)
ECAT_INT: U5.45 (PE15)
ECAT_MISO: U5.30 (PA6)
ECAT_MOSI: U5.31 (PA7)
ECAT_RST: U5.54 (PB15)
ECAT_SCK: U5.29 (PA5)
ECAT_SYNC0: U5.44 (PE14)
ECAT_SYNC1: U5.43 (PE13)
ENC0_A_DIR: U5.85 (PD4)
ENC0_A_Data: U5.18 (PC3_C), U5.39 (PE9)
ENC0_B_DIR: U5.55 (PD8)
ENC0_B_Data: U5.41 (PE11), U5.68 (PA9)
ENC0_Z_Data: U5.81 (PD0)
ENC1_A_DIR: U5.86 (PD5)
ENC1_A_Data: U5.36 (PB2), U5.77 (PA15)
ENC1_B_DIR: U5.56 (PD9)
ENC1_B_Data: U5.23 (PA1), U5.78 (PC10)
ENC1_Z_Data: U5.82 (PD1)
ENC2_A_DIR: U5.87 (PD6)
ENC2_A_Data: U5.5 (PE6), U5.63 (PC6)
ENC2_B_DIR: U5.57 (PD10)
ENC2_B_Data: U5.1 (PE2), U5.64 (PC7)
ENC2_Z_Data: U5.83 (PD2)
ENC3_A_DIR: U5.88 (PD7)
ENC3_A_Data: U5.59 (PD12)
ENC3_B_DIR: U5.58 (PD11)
ENC3_B_Data: U5.60 (PD13)
ENC3_Z_Data: U5.84 (PD3)
GND: C30.1, C31.1, C32.1, C33.2, C34.2, C35.2, C36.1, C37.1, C38.1, C40.1, C41.1, C43.1, J4.5, R34.2, U5.10 (VSS), U5.19 (VSSA), U5.26 (VSS), U5.49 (VSS), U5.74 (VSS), U5.99 (VSS), Y2.2, Y2.4
I2C1_SCL: U5.92 (PB6)
I2C1_SDA: U5.93 (PB7)
I2C2_SCL: U5.46 (PB10)
I2C2_SDA: U5.47 (PB11)
unnamed: C30.2, U5.12 (PH0), Y2.3
unnamed: C31.2, U5.13 (PH1), Y2.1
unnamed: C32.2, R33.2, U5.20 (VREF+)
unnamed: C33.1, U5.48 (VCAP)
unnamed: C34.1, U5.73 (VCAP)
unnamed: R34.1, U5.94 (BOOT0)
RST: C35.1, J4.3, U5.14 (NRST)
SWCLK: J4.4, U5.76 (PA14)
SWDIO: J4.2, U5.72 (PA13)
SWO: J4.6, U5.89 (PB3)
VDDA: C36.2, L4.1, R33.1, U5.21 (VDDA)
